gservers/boxduino/Gallery/6.2.AutoStatistics.jpg

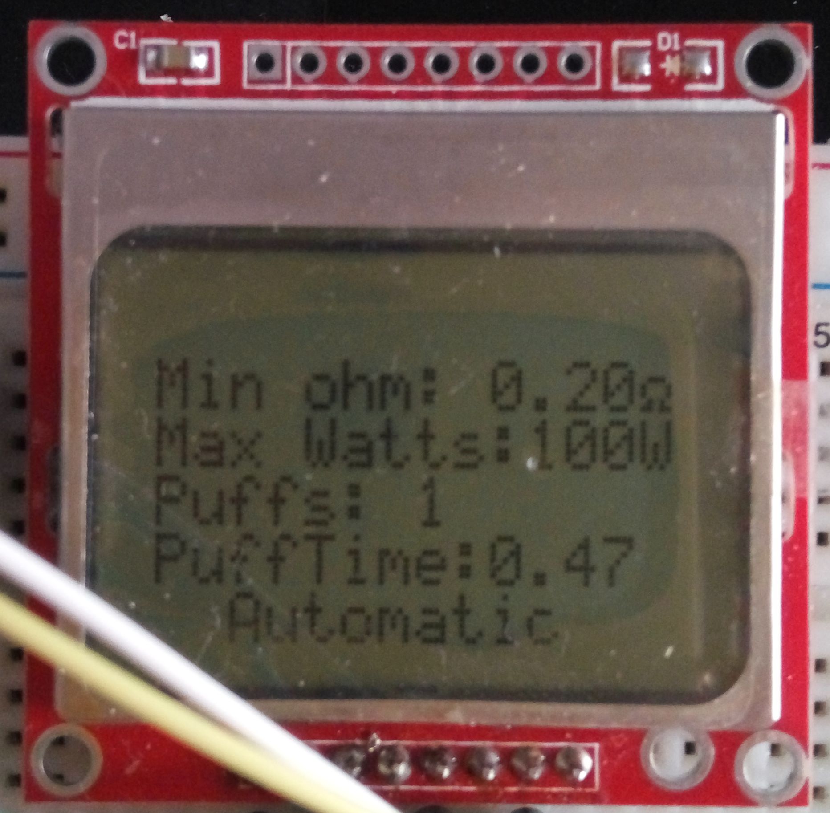
Gallery/6.2.AutoStatistics.jpg
