gservers/boxduino/Gallery/7.2.Breadboard.jpg

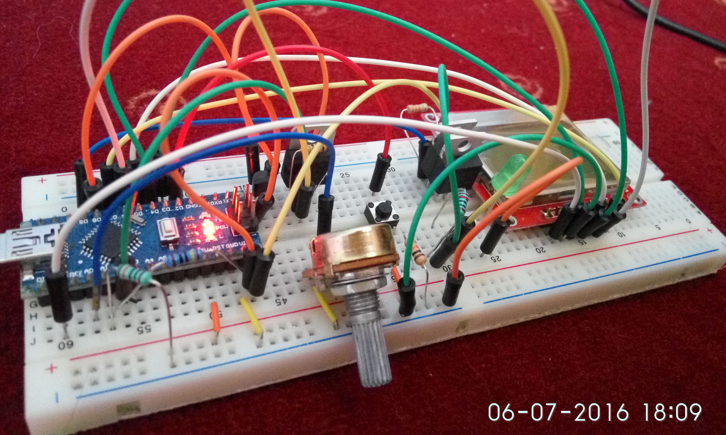
Gallery/7.2.Breadboard.jpg
