gservers/boxduino/Gallery/2.StartupManual.jpg

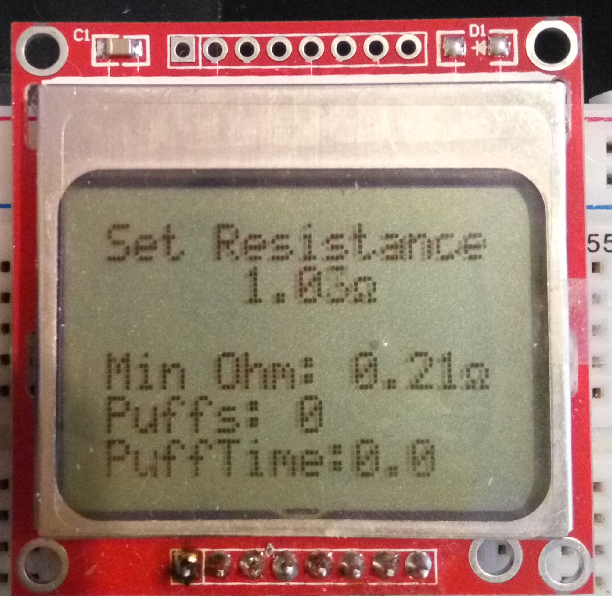
Gallery/2.StartupManual.jpg
